TinyCircuits/TinyCircuits-Pocket-Arcade-ASM2026/images/Pocket-Arcade-Tutorial-Image-01.jpg

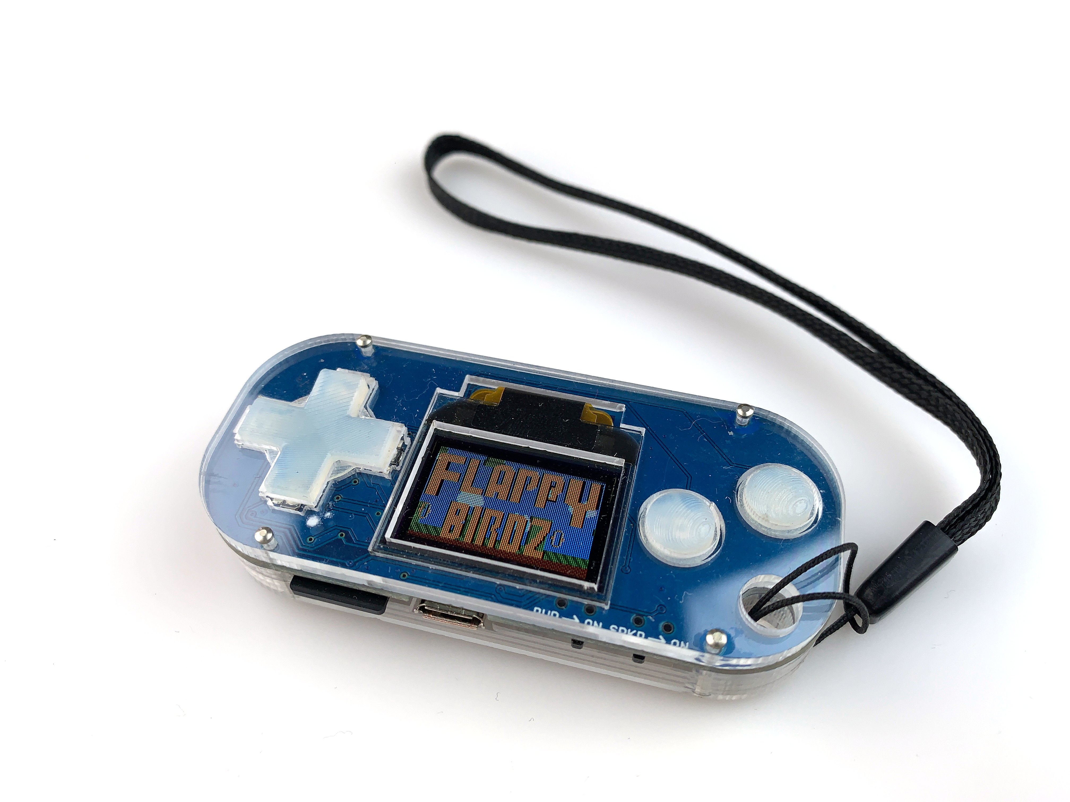
images/Pocket-Arcade-Tutorial-Image-01.jpg
