TinyCircuits/TinyCircuits-Pocket-Arcade-ASM2026/images/Pocket-Arcade-Tutorial-Image-02.png

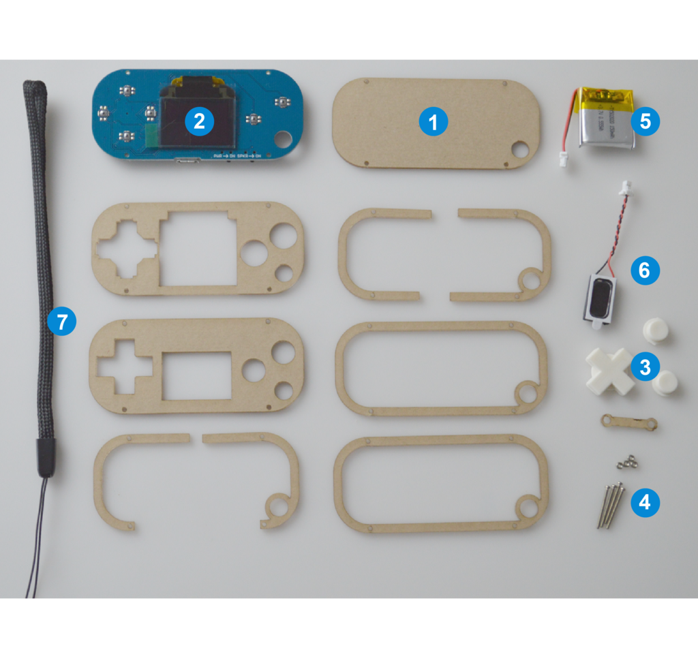
images/Pocket-Arcade-Tutorial-Image-02.png
