TinyCircuits/TinyCircuits-Pocket-Arcade-ASM2026/images/Pocket-Arcade-Tutorial-Image-03.jpg

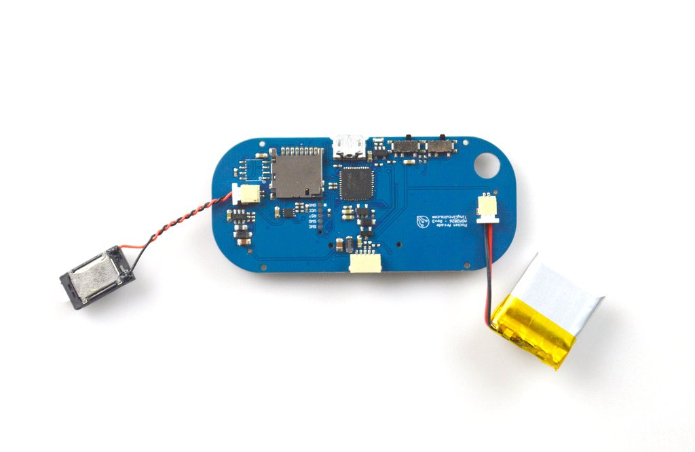
images/Pocket-Arcade-Tutorial-Image-03.jpg
