TinyCircuits/TinyCircuits-Pocket-Arcade-ASM2026/images/Pocket-Arcade-Tutorial-Image-05.jpg

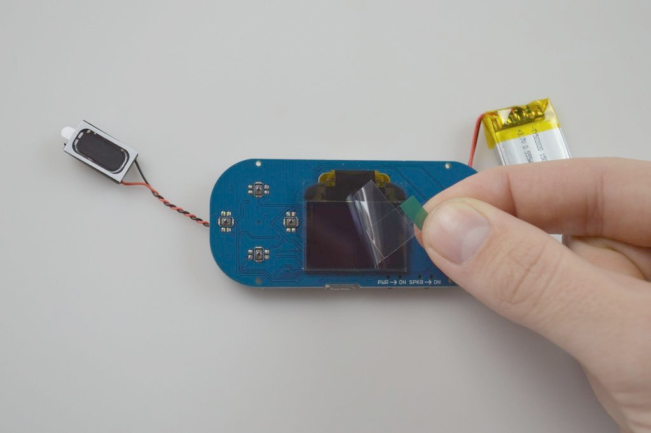
images/Pocket-Arcade-Tutorial-Image-05.jpg
