TinyCircuits/TinyCircuits-Pocket-Arcade-ASM2026/images/Pocket-Arcade-Tutorial-Image-06.jpg

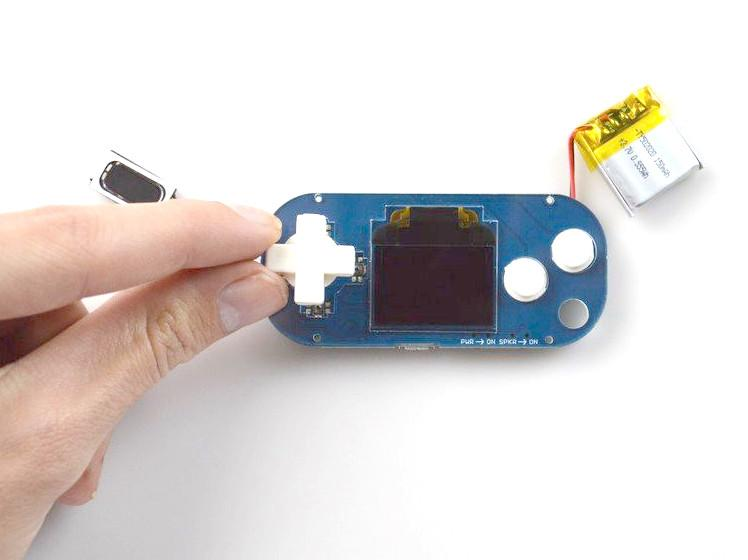
images/Pocket-Arcade-Tutorial-Image-06.jpg
